alexlafetra/tamo/tamo/src/sprites.h

//Need to use drawmode = vertical in image2cpp
//these are the bitmap graphics shared between all creatures!

#include "creatures/tamo.h"
#include "creatures/porcini.h"
#include "creatures/bug.h"

/*
----------------------------------

 Talking icons

----------------------------------
*/

// 'bubble', 12x11px
const unsigned char epd_bitmap_bubble [] PROGMEM = {
	0x00, 0x7c, 0x82, 0x01, 0x01, 0x01, 0x01, 0x01, 0x01, 0x01, 0x82, 0x7c, 0x02, 0x05, 0x04, 0x02, 
	0x02, 0x01, 0x01, 0x01, 0x01, 0x01, 0x00, 0x00
};
// 'low_battery_bubble', 7x7px
const unsigned char epd_bitmap_low_battery_bubble [] PROGMEM = {
	0x1c, 0x22, 0x32, 0x2a, 0x26, 0x22, 0x3e
};
// 'face1', 7x7px
const unsigned char epd_bitmap_face1 [] PROGMEM = {
	0x04, 0x04, 0x10, 0x10, 0x10, 0x04, 0x04
};
// 'cash_bubble', 7x7px
const unsigned char epd_bitmap_cash_bubble [] PROGMEM = {
	0x00, 0x24, 0x2a, 0x7f, 0x2a, 0x12, 0x00
};
// 'note', 7x7px
const unsigned char epd_bitmap_note [] PROGMEM = {
	0x00, 0x30, 0x30, 0x1e, 0x02, 0x00, 0x00
};
// 'face2', 7x7px
const unsigned char epd_bitmap_face2 [] PROGMEM = {
	0x04, 0x04, 0x30, 0x30, 0x30, 0x04, 0x04
};
// 'hungry_bubble', 7x7px
const unsigned char epd_bitmap_hungry_bubble [] PROGMEM = {
	0x1c, 0x3e, 0x36, 0x22, 0x08, 0x00, 0x08
};
// 'skull_bubble', 7x7px
const unsigned char epd_bitmap_skull_bubble [] PROGMEM = {
	0x0c, 0x3a, 0x1e, 0x36, 0x1e, 0x3a, 0x0c
};
// 'dog_bubble', 7x7px
const unsigned char epd_bitmap_dog_bubble [] PROGMEM = {
	0x0e, 0x1f, 0x3a, 0x2e, 0x27, 0x2a, 0x1c
};
// 'gun_bubble', 7x7px
const unsigned char epd_bitmap_gun_bubble [] PROGMEM = {
	0x0c, 0x0c, 0x1c, 0x0c, 0x3a, 0x38, 0x00
};
// 'broken_heart_bubble', 7x7px
const unsigned char epd_bitmap_broken_heart_bubble [] PROGMEM = {
	0x00, 0x0e, 0x1e, 0x00, 0x38, 0x1c, 0x0c
};
// 'heart_bubble', 7x7px
const unsigned char epd_bitmap_heart_bubble [] PROGMEM = {
	0x00, 0x0e, 0x1e, 0x3c, 0x1e, 0x0e, 0x00
};

const unsigned char* const talking_heartbreak[3] PROGMEM = {
	epd_bitmap_bubble,
	epd_bitmap_heart_bubble,
	epd_bitmap_broken_heart_bubble
};
const unsigned char* const talking_low_battery[2] PROGMEM = {
	epd_bitmap_bubble,
	epd_bitmap_low_battery_bubble
};
const unsigned char* const talking_love[2] PROGMEM = {
	epd_bitmap_bubble,
	epd_bitmap_heart_bubble
};
  const unsigned char* const talking_death[2] PROGMEM = {
	epd_bitmap_bubble,
	epd_bitmap_skull_bubble
  };
  const unsigned char* const talking_hunger[2] PROGMEM = {
	epd_bitmap_bubble,
	epd_bitmap_hungry_bubble
  };
  const unsigned char* const talking_revenge[2] PROGMEM = {
	epd_bitmap_bubble,
	epd_bitmap_gun_bubble
  };
  const unsigned char* const talking_me[3] PROGMEM = {
	  epd_bitmap_bubble,
	  epd_bitmap_face1,
	  epd_bitmap_face2
  };
  const unsigned char* const talking_music[2] PROGMEM = {
	  epd_bitmap_bubble,
	  epd_bitmap_note
  };
  const unsigned char* const talking_cash[2] PROGMEM = {
	  epd_bitmap_bubble,
	  epd_bitmap_cash_bubble
  };
  const unsigned char* const talking_dog[2] PROGMEM = {
	  epd_bitmap_bubble,
	  epd_bitmap_dog_bubble
  };

/*
----------------------------------

 	Poop

----------------------------------
*/
// 'poop1', 16x16px
const unsigned char epd_bitmap_poop1 [] PROGMEM = {
	0x00, 0x00, 0x00, 0x00, 0x20, 0x50, 0x00, 0x80, 0xc0, 0x80, 0x00, 0x00, 0x00, 0x80, 0x00, 0x00, 
	0x00, 0x00, 0x70, 0x48, 0x54, 0x54, 0x53, 0x55, 0x54, 0x41, 0x42, 0x4c, 0x50, 0x62, 0x01, 0x00
};
// 'poop4', 16x16px
const unsigned char epd_bitmap_poop4 [] PROGMEM = {
	0x00, 0x00, 0x00, 0x00, 0x0a, 0x04, 0x00, 0x80, 0xc0, 0x80, 0x00, 0x00, 0x00, 0x20, 0x50, 0x00, 
	0x00, 0x00, 0x70, 0x48, 0x54, 0x54, 0x53, 0x55, 0x54, 0x41, 0x42, 0x4c, 0x50, 0x60, 0x00, 0x00
};

const unsigned char* const poopAnim[2] PROGMEM = {
	epd_bitmap_poop1,
	epd_bitmap_poop4
};

/*
----------------------------------

 	Sleep Z's

----------------------------------
*/

// 'sleep_1', 16x16px
const unsigned char epd_bitmap_sleep_1 [] PROGMEM = {
	0x00, 0x40, 0x40, 0xc0, 0x00, 0x20, 0xa0, 0x60, 0x00, 0x40, 0x40, 0xc0, 0x00, 0x20, 0xa0, 0x60, 
	0x00, 0x06, 0x05, 0x04, 0x00, 0x03, 0x02, 0x02, 0x00, 0x06, 0x05, 0x04, 0x00, 0x03, 0x02, 0x02
};
// 'sleep_3', 16x16px
const unsigned char epd_bitmap_sleep_3 [] PROGMEM = {
	0x00, 0x20, 0xa0, 0x60, 0x00, 0x40, 0x40, 0xc0, 0x00, 0x20, 0xa0, 0x60, 0x00, 0x40, 0x40, 0xc0, 
	0x00, 0x03, 0x02, 0x02, 0x00, 0x06, 0x05, 0x04, 0x00, 0x03, 0x02, 0x02, 0x00, 0x06, 0x05, 0x04
};
// Array of all bitmaps for convenience. (Total bytes used to store images in PROGMEM = 96)
const unsigned char* const sleeping_sprite[2] PROGMEM = {
	epd_bitmap_sleep_1,
	epd_bitmap_sleep_3
};

/*
----------------------------------

 	Death/Tombstone

----------------------------------
*/

// 'tombstone1', 16x16px
const unsigned char epd_bitmap_tombstone1 [] PROGMEM = {
	0x04, 0xf0, 0xfc, 0x1e, 0x06, 0x62, 0x92, 0x12, 0x22, 0x12, 0x92, 0x62, 0x04, 0x18, 0xe0, 0x02, 
	0x00, 0x7f, 0x7f, 0x80, 0x80, 0xb8, 0x88, 0x81, 0xba, 0x81, 0xb8, 0x98, 0x80, 0x80, 0x7f, 0x00
};
// 'tombstone2', 16x16px
const unsigned char epd_bitmap_tombstone2 [] PROGMEM = {
	0x02, 0xf0, 0xfc, 0x1e, 0x06, 0x62, 0x92, 0x12, 0x22, 0x12, 0x92, 0x62, 0x04, 0x18, 0xe0, 0x04, 
	0x00, 0x7f, 0x7f, 0x80, 0x80, 0xb8, 0x88, 0x81, 0xba, 0x81, 0xb8, 0x98, 0x80, 0x80, 0x7f, 0x00
};

const unsigned char* const death_sprite[2] PROGMEM = {
	epd_bitmap_tombstone1,
	epd_bitmap_tombstone2
};

/*
----------------------------------

 	 Egg hatching

----------------------------------
*/

// 'egg1', 16x16px
const unsigned char epd_bitmap_egg1 [] PROGMEM = {
	0x00, 0x00, 0x00, 0x00, 0xc0, 0x20, 0x10, 0x10, 0x10, 0x10, 0x20, 0xc0, 0x00, 0x00, 0x00, 0x00, 
	0x00, 0x00, 0x00, 0x3f, 0x40, 0x80, 0x80, 0x80, 0x80, 0x80, 0x80, 0x40, 0x3f, 0x00, 0x00, 0x00
};
// 'egg2', 16x16px
const unsigned char epd_bitmap_egg2 [] PROGMEM = {
	0x00, 0x00, 0x00, 0x00, 0xc0, 0x20, 0x50, 0x90, 0x10, 0x10, 0x20, 0xc0, 0x00, 0x00, 0x00, 0x00, 
	0x00, 0x00, 0x00, 0x3f, 0x40, 0x80, 0x82, 0x80, 0x80, 0x80, 0x84, 0x40, 0x3f, 0x00, 0x00, 0x00
};
// 'egg3', 16x16px
const unsigned char epd_bitmap_egg3 [] PROGMEM = {
	0x00, 0x00, 0x00, 0x00, 0xc0, 0x20, 0x50, 0x90, 0x90, 0x90, 0x20, 0xc0, 0x00, 0x00, 0x00, 0x00, 
	0x00, 0x00, 0x00, 0x3f, 0x48, 0x84, 0x8a, 0x80, 0xc0, 0xa0, 0x9d, 0x40, 0x3f, 0x00, 0x00, 0x00
};
// 'egg4', 16x16px
const unsigned char epd_bitmap_egg4 [] PROGMEM = {
	0x00, 0x02, 0x04, 0x00, 0x00, 0xc0, 0x20, 0x40, 0x40, 0x20, 0xc0, 0x00, 0x00, 0x04, 0x02, 0x00, 
	0x00, 0x40, 0x20, 0x00, 0x00, 0x01, 0x02, 0x04, 0x04, 0x02, 0x01, 0x00, 0x00, 0x20, 0x40, 0x00
};

const unsigned char* const egg_sprite[4] PROGMEM = {
	epd_bitmap_egg1,
	epd_bitmap_egg2,
	epd_bitmap_egg3,
	epd_bitmap_egg4
};

// 'food_1', 16x13px
const unsigned char epd_bitmap_food_1 [] PROGMEM = {
	0xf0, 0xf8, 0xfc, 0xee, 0xd6, 0xef, 0xff, 0xff, 0xff, 0xdf, 0x7f, 0xf6, 0xfe, 0xfc, 0xf8, 0xf0, 
	0x01, 0x03, 0x06, 0x0f, 0x0f, 0x1d, 0x1f, 0x1f, 0x1f, 0x1e, 0x1d, 0x0e, 0x0f, 0x07, 0x03, 0x01
};
// 'food_2', 16x13px
const unsigned char epd_bitmap_food_2 [] PROGMEM = {
	0x00, 0x10, 0x00, 0x02, 0x22, 0x07, 0x8f, 0xff, 0xff, 0xdf, 0x7f, 0xf6, 0xfe, 0xfc, 0xf8, 0xf0, 
	0x00, 0x01, 0x06, 0x0e, 0x0e, 0x1d, 0x1f, 0x1f, 0x1f, 0x1e, 0x1d, 0x0e, 0x0f, 0x07, 0x03, 0x01
};
// 'food_3', 16x13px
const unsigned char epd_bitmap_food_3 [] PROGMEM = {
	0x00, 0x10, 0x00, 0x02, 0x42, 0x07, 0x0f, 0x1f, 0x9f, 0x1f, 0x3f, 0x76, 0xfe, 0xfc, 0xf8, 0xf0, 
	0x00, 0x00, 0x00, 0x00, 0x00, 0x00, 0x00, 0x00, 0x00, 0x00, 0x00, 0x00, 0x03, 0x07, 0x03, 0x01
};
// 'food_4', 16x13px
const unsigned char epd_bitmap_food_4 [] PROGMEM = {
	0x00, 0x10, 0x00, 0x02, 0x42, 0x07, 0x0f, 0x1f, 0x9f, 0x1f, 0x3f, 0x36, 0x1e, 0x1c, 0x58, 0x10, 
	0x00, 0x00, 0x00, 0x00, 0x00, 0x00, 0x00, 0x00, 0x00, 0x00, 0x00, 0x04, 0x00, 0x00, 0x00, 0x00
};
// 'food_5', 16x13px
const unsigned char epd_bitmap_food_5 [] PROGMEM = {
	0x00, 0x10, 0x00, 0x00, 0x00, 0x00, 0x00, 0x10, 0x00, 0x00, 0x01, 0x00, 0x00, 0x00, 0x40, 0x00, 
	0x00, 0x00, 0x00, 0x00, 0x00, 0x00, 0x00, 0x00, 0x00, 0x00, 0x00, 0x04, 0x00, 0x00, 0x00, 0x00
};

const unsigned char* const food_animation[5] PROGMEM = {
	epd_bitmap_food_1,
	epd_bitmap_food_2,
	epd_bitmap_food_3,
	epd_bitmap_food_4,
	epd_bitmap_food_5
};


/*
----------------------------------

 	 Titlescreen/'hello' stuff

----------------------------------
*/

// 'palestine', 29x16px
const unsigned char free_palestine_bmp [] PROGMEM = {
	0x00, 0x00, 0x00, 0x00, 0x00, 0x00, 0x19, 0x14, 0x1d, 0x50, 0x10, 0x5c, 0x00, 0x40, 0x3c, 0x10, 
	0x14, 0x14, 0x0c, 0x14, 0x10, 0x0f, 0x00, 0x1f, 0x00, 0x00, 0x00, 0x00, 0x00, 0x40, 0x80, 0x88, 
	0x80, 0x70, 0x20, 0xa0, 0x10, 0xa0, 0x20, 0x2f, 0x30, 0x28, 0x28, 0x30, 0x20, 0x30, 0x20, 0x30, 
	0x20, 0x38, 0x20, 0x1f, 0x20, 0x38, 0x25, 0x38, 0x20, 0x1f
};

// 'hi', 16x16px
// const unsigned char bitmap_hi [] PROGMEM = {
// 	0x00, 0x00, 0x00, 0x80, 0x60, 0x00, 0x00, 0x00, 0x00, 0x00, 0x00, 0x00, 0x00, 0x40, 0x00, 0x00, 
// 	0x00, 0x00, 0x02, 0x07, 0x01, 0x06, 0x04, 0x02, 0x04, 0x04, 0x02, 0x03, 0x04, 0x04, 0x00, 0x00
// };

// // 'mai', 19x16px
// const unsigned char bitmap_mai [] PROGMEM = {
// 	0x00, 0x00, 0x80, 0x00, 0x80, 0x00, 0x00, 0x00, 0x00, 0x80, 0x80, 0x00, 0x00, 0x00, 0x00, 0x00, 
// 	0x00, 0x40, 0x00, 0x02, 0x07, 0x00, 0x07, 0x00, 0x07, 0x04, 0x02, 0x05, 0x04, 0x03, 0x04, 0x04, 
// 	0x04, 0x02, 0x03, 0x04, 0x04, 0x00
// };
// // 'li', 18x16px
// const unsigned char bitmap_li [] PROGMEM = {
// 	0x00, 0x00, 0x00, 0x00, 0x00, 0x00, 0x80, 0xe0, 0x00, 0x00, 0x00, 0x00, 0x00, 0x00, 0x40, 0x00, 
// 	0x00, 0x00, 0x00, 0x00, 0x00, 0x04, 0x04, 0x02, 0x03, 0x04, 0x04, 0x04, 0x04, 0x02, 0x03, 0x04, 
// 	0x04, 0x00, 0x00, 0x00
// };


  //intro
  // oled.clear();
  // oled.bitmap2x(22,0,38,2,bitmap_hi);
  // delay(600);
  // oled.bitmap2x(20,0,39,2,bitmap_mai);
  // delay(600);
  // oled.bitmap2x(20,0,39,2,bitmap_li);
  // delay(600);


//448 bytes per creature (7 emotions, 2 frames per emotion)

//you need 254 bytes for a third creature
