alexlafetra/tamo/tamo/src/utils.cpp

#include "spritesheet.h"
#include <Arduino.h>
#include <Wire.h>
#include <avr/sleep.h>
#include <avr/interrupt.h>
#include "Display.h"
#include "utils.h"
#include "Tamo.h"
#include "communication.h"

// #define BUTTON_PIN PIN_PA2
// #define LED_1 PIN_PA6
// #define LED_0 PIN_PC0
// #define UART_RX_PIN PIN_PB3
// #define UART_TX_PIN PIN_PB2

#define BUTTON_PIN PIN_PB4
#define LED_0 PIN_PC1
#define LED_1 PIN_PA6
#define LED_2 PIN_PC0

#define UART_RX_PIN PIN_PB3
#define UART_TX_PIN PIN_PB2

#define ULTRA_LONG_PRESS_TIME 5000
#define LONG_PRESS_TIME 1000
#define DOUBLE_CLICK_TIME 200

// these prob don't need to be volatile, since readButtons() isn't called from an interrupt
volatile bool BUTTON = false;
volatile bool LONG_PRESS = false;
volatile bool ULTRA_LONG_PRESS = false;
volatile bool DOUBLE_CLICK = false;
volatile bool SINGLE_CLICK = false;

volatile uint32_t timeOfLastButtonPress = 0;
uint32_t lastTime = 0;

uint8_t get_sprite_data(uint16_t offset){
  // super hacky
  // if(tamo.identity == CUSTOM_SPRITE){
  //   return customSpriteData[offset%64];
  // }
  // else
  return spritesheet[offset];
}

bool itsbeen(uint32_t time){
  return((millis()-lastTime)>time);  
}

//returns a random number from 0 - range, exclusive
uint8_t randomInt(uint8_t range){
  return millis()%range;
}

uint16_t readVcc() {

  // from: https://github.com/SpenceKonde/megaTinyCore/blob/master/megaavr/extras/Ref_Analog.md
  analogReference(INTERNAL1V1); // set reference to the desired voltage, and set that as the ADC reference.
  analogReference(VDD); // Set the ADC reference to VDD. Voltage selected previously is still the selected, just not set as the ADC reference.
  uint16_t val =  analogRead(ADC_INTREF); // proceed to measure the analog reference.
  return val;
}

//reading inputs
void checkInput(){
  checkInput(true);
}
void checkInput(bool updateLEDs){

  checkSerialConnection();
  uint8_t val = digitalRead(BUTTON_PIN);
  // uint8_t val = (PINB & (1<<PB1));//check the value from the PB1 register
  //if the button is pressed
  if(!val){
    //if the button wasn't previously pressed, then it's a fresh press
    if(!BUTTON){
      if((millis()-timeOfLastButtonPress) < (DOUBLE_CLICK_TIME)){
        DOUBLE_CLICK = true;
      }
      else{
        DOUBLE_CLICK = false;
        SINGLE_CLICK = false;
      }
      timeOfLastButtonPress = millis();
    }
    //turn on the LED
    if(updateLEDs)
      digitalWrite(LED_1,true);
    //set the button flag
    BUTTON = true;
    //check to see if it's been held
    if((millis() - timeOfLastButtonPress) > (LONG_PRESS_TIME) ){
      if(LONG_PRESS)
        ULTRA_LONG_PRESS = true;
      else
        LONG_PRESS = true;
      timeOfLastButtonPress = millis();
    }
  }
  //if the button is released
  else{
    //turn off the LED
    if(updateLEDs)
      digitalWrite(LED_1,false);
    //if the button *was* held, then you just released it
    if(BUTTON){
      //if it was held for a while, it's a long press
      if((millis() - timeOfLastButtonPress) > (LONG_PRESS_TIME) ){
        LONG_PRESS = true;
        DOUBLE_CLICK = false;
        SINGLE_CLICK = false;
        ULTRA_LONG_PRESS = false;
        timeOfLastButtonPress = millis();
      }
      //if it wasn't, then it's a single click
      else{
        SINGLE_CLICK = true;
        LONG_PRESS = false;
        DOUBLE_CLICK = false;
        ULTRA_LONG_PRESS = false;
        timeOfLastButtonPress = millis();
      }
    }
    //if the button wasn't pressed down before, and isn't pressed down now, then don't do anything
    else{
      SINGLE_CLICK = false;
      LONG_PRESS = false;
      DOUBLE_CLICK = false;
      ULTRA_LONG_PRESS = false;
    }
    BUTTON = false;
  }
}

void sleepHardware(){
  //set pin change interrupt on the button pin
  //from: https://github.com/SpenceKonde/megaTinyCore/blob/master/megaavr/extras/Ref_PinInterrupts.md
  PORTA.PIN2CTRL|= PORT_ISC_FALLING_gc;

  //turn off ADC
  ADC0.CTRLA &= ~ADC_ENABLE_bm;
  //turn off OLED, LEDs
  oled.off();
  digitalWrite(LED_1,false);
  digitalWrite(LED_0,false);
  
  sleep_enable();
  sleep_cpu();
}

void wakeHardware(){
  sleep_disable();                       // first thing after waking from sleep: disable sleep
  //turn off interrupt
  PORTA.PIN2CTRL &= (0b11111000 | PORT_ISC_INTDISABLE_gc);
  
  //reset button states, so wakeup doesn't trigger anything
  SINGLE_CLICK = false;
  LONG_PRESS = false;
  lastTime = millis();

  //turn on ADC
  ADC0.CTRLA |= ADC_ENABLE_bm;

  oled.on();//turn screen back on
}
